Vigneshsundar128/SmartMonitor/PowerMonitor/webserver.cpp

#include "webserver.h"
#include "wifi_manager.h"
#include "pzem_driver.h"
#include <ESPAsyncTCP.h>
#include <ESPAsyncWebServer.h>
#include <ElegantOTA.h>
#include "webpage.h"
#include "config.h"

AsyncWebServer server(Config::Web::kPort); // single global server used by OTA and web UI

void webserver_begin() {
  server.on("/", HTTP_GET, [](AsyncWebServerRequest *request){
    request->send_P(200, "text/html", index_html, processor);
  });

  // data route serves JSON updated by pzem_driver
  server.on("/data", HTTP_GET, [](AsyncWebServerRequest *request){
    String json = "{";
    json += "\"voltage\":\"" + String(isnan(pzem_get_voltage()) ? "Error" : String(pzem_get_voltage(), 1)) + "\",";
    json += "\"current\":\"" + String(isnan(pzem_get_current()) ? "Error" : String(pzem_get_current(), 2)) + "\",";
    json += "\"power\":\"" + String(isnan(pzem_get_power()) ? "Error" : String(pzem_get_power(), 1)) + "\",";
    json += "\"energy\":\"" + String(isnan(pzem_get_energy()) ? "Error" : String(pzem_get_energy(), 3)) + "\",";
    json += "\"frequency\":\"" + String(isnan(pzem_get_frequency()) ? "Error" : String(pzem_get_frequency(), 1)) + "\",";
    json += "\"pf\":\"" + String(isnan(pzem_get_pf()) ? "Error" : String(pzem_get_pf(), 2)) + "\"";
    json += "}";
    request->send(200, "application/json", json);
  });

  ElegantOTA.begin(&server); // Start ElegantOTA
  server.begin();
  Serial.println("HTTP server started");
}
